RobSteele49/piStepperMotorControl/photos/IMG_4492.JPG

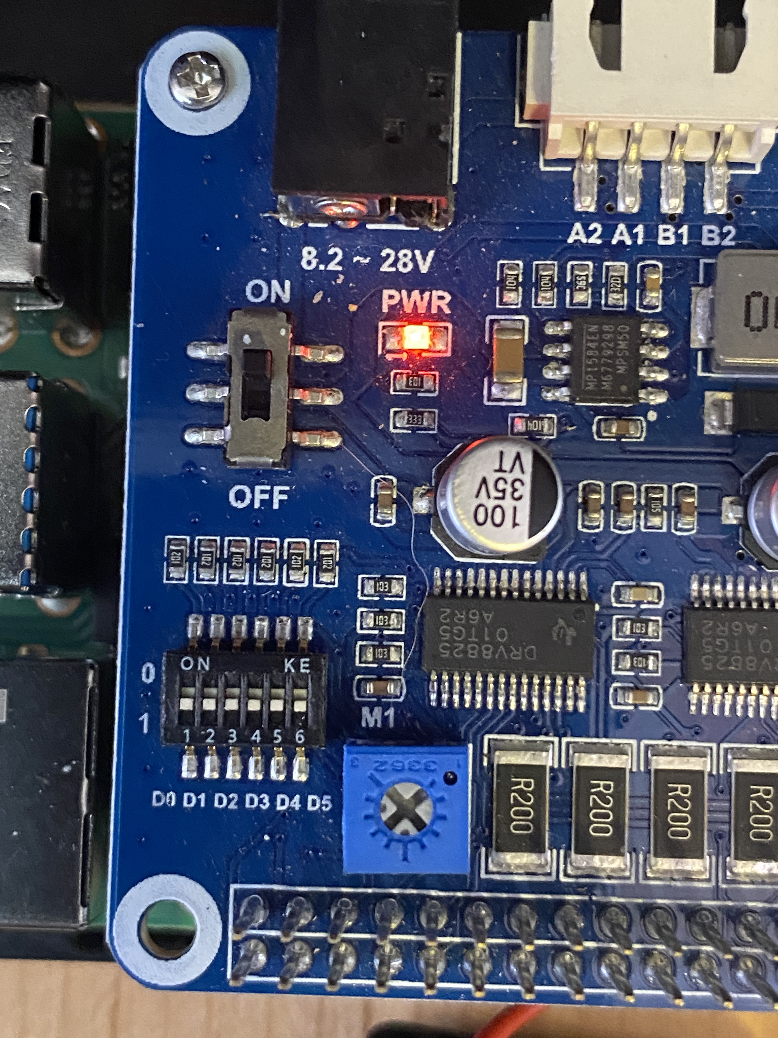
photos/IMG_4492.JPG
