RobSteele49/piStepperMotorControl/drivers/drv8825-minimal-chatgpt/motor2Test.py

# Filename: motor2Test.py

from DRV8825 import DRV8825
import time

motor2 = DRV8825(dir_pin=24, step_pin=18, enable_pin=4)

motor2.move(800, direction=True)    # quarter turn
time.sleep(1)
motor2.move(800, direction=False)
time.sleep(1)

# Since I am current set for 1/16 microsteps per pulse 3220 steps are
# required for one revolution

motor2.move(3200, True)
time.sleep(1)
motor2.move(3200, False)
time.sleep(1)
