RobSteele49/piStepperMotorControl/photos/IMG_4491.JPG

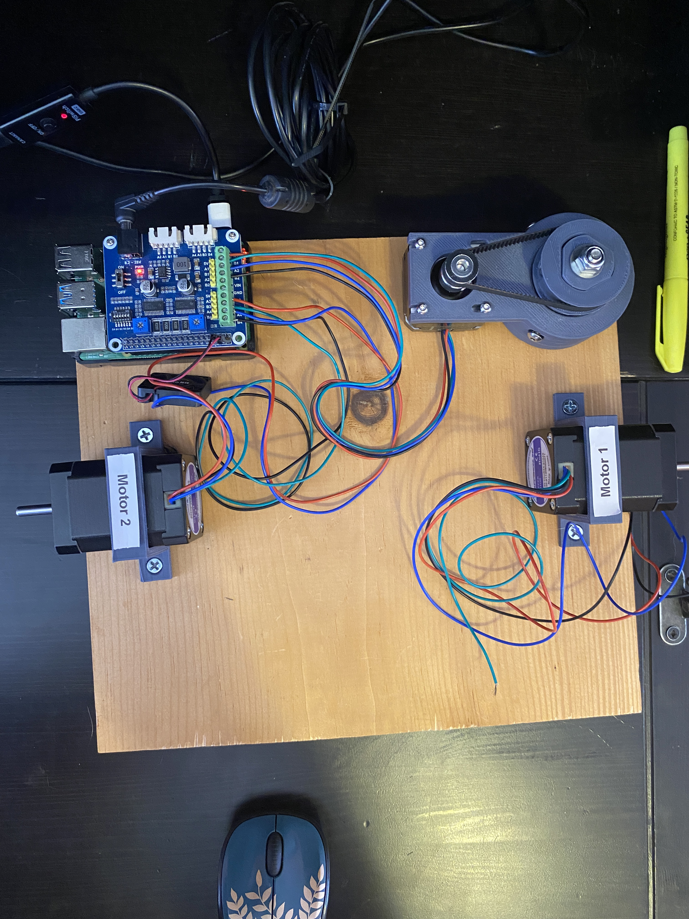
photos/IMG_4491.JPG
