RobSteele49/piStepperMotorControl/photos/IMG_4500.JPG

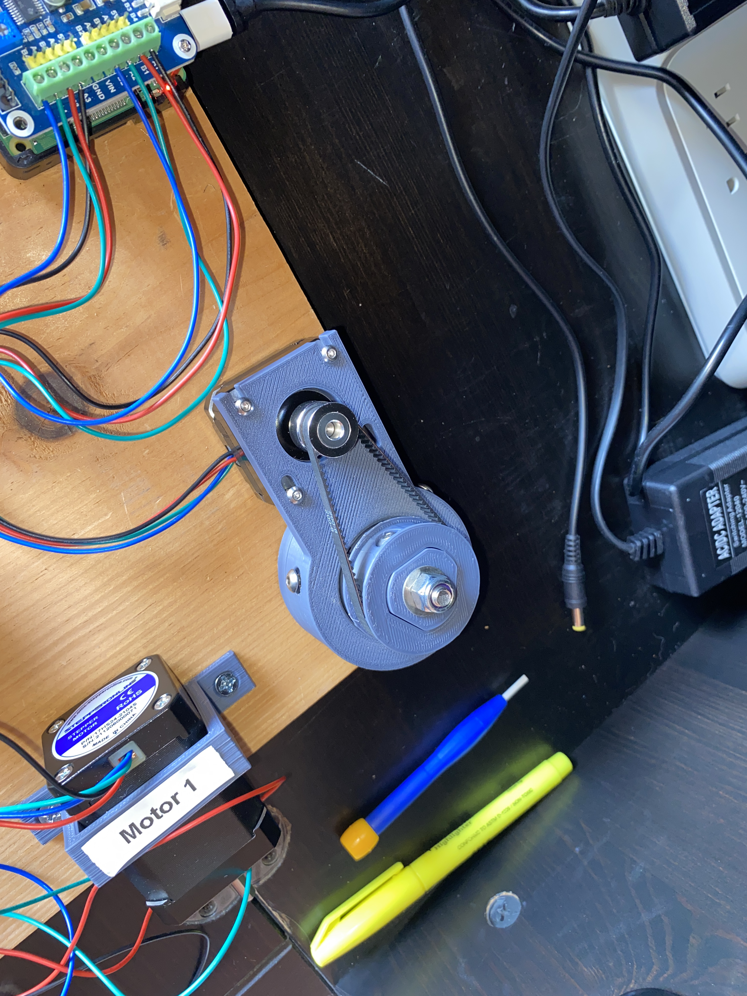
photos/IMG_4500.JPG
